tpar0015/4191-Robot/data/labelled/g_bl_ca_4.jpg

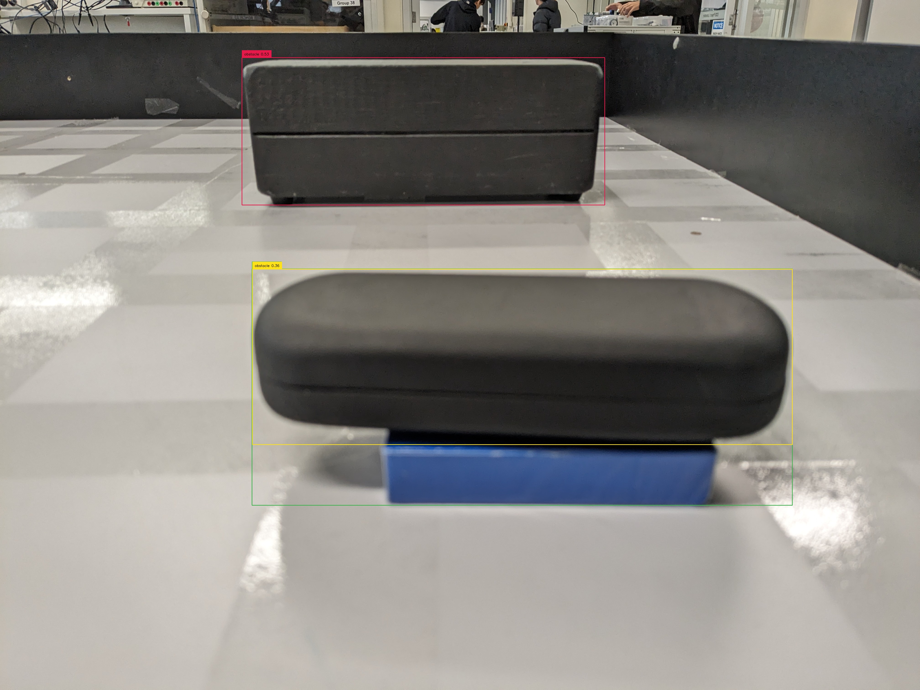
data/labelled/g_bl_ca_4.jpg
