tpar0015/4191-Robot/camera_img/camera3.jpg

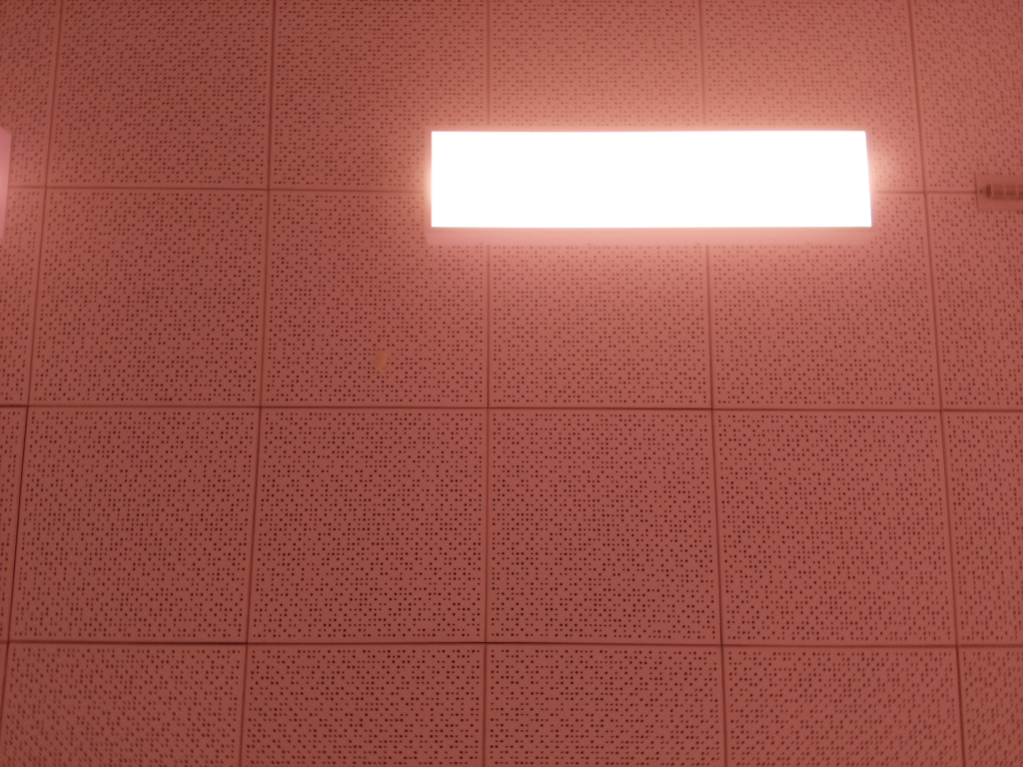
camera_img/camera3.jpg
