tpar0015/4191-Robot/camera_img/tes2/camera4.jpg

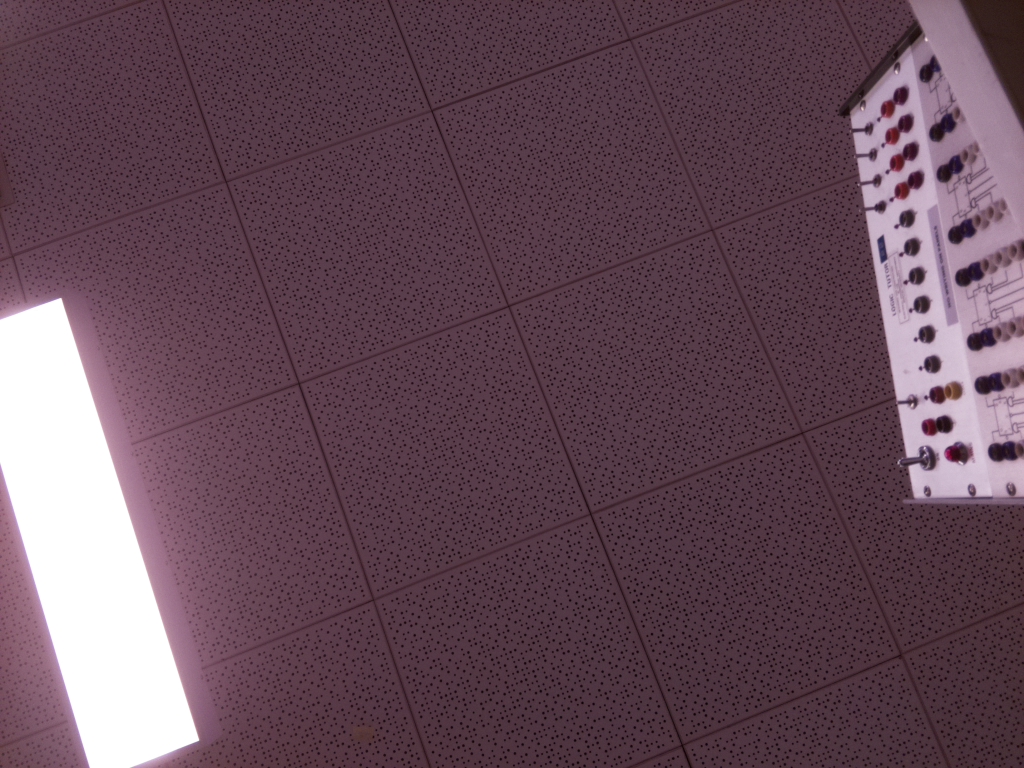
camera_img/tes2/camera4.jpg
