tpar0015/4191-Robot/Corner Detection/1.jpeg

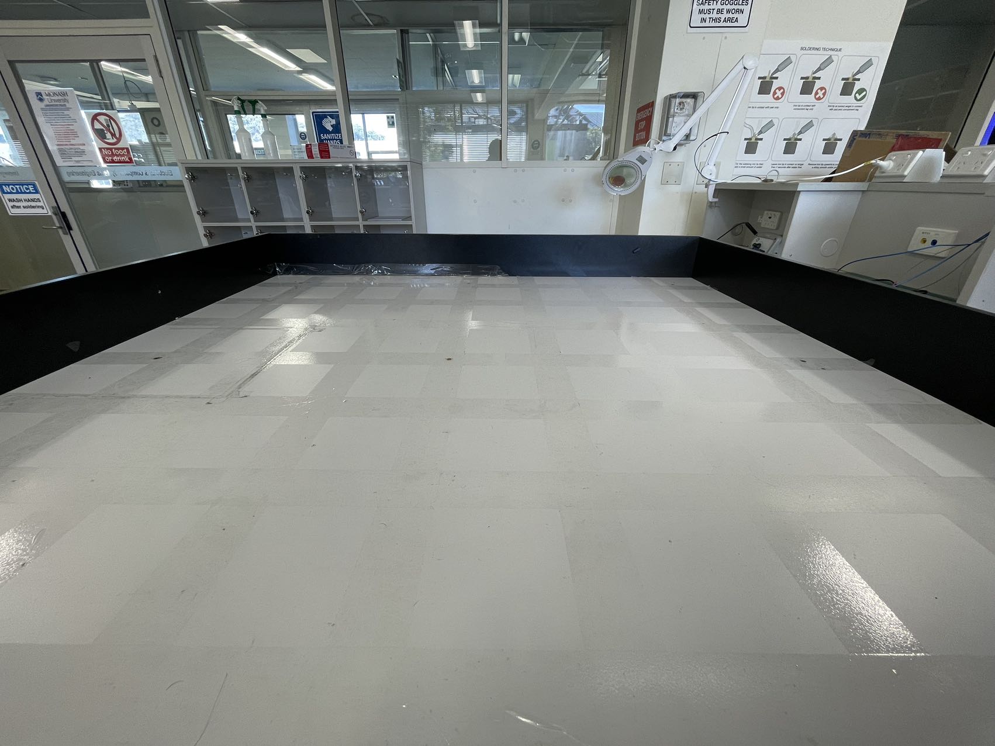
Corner Detection/1.jpeg
