tpar0015/4191-Robot/Corner Detection/arena_2.jpeg

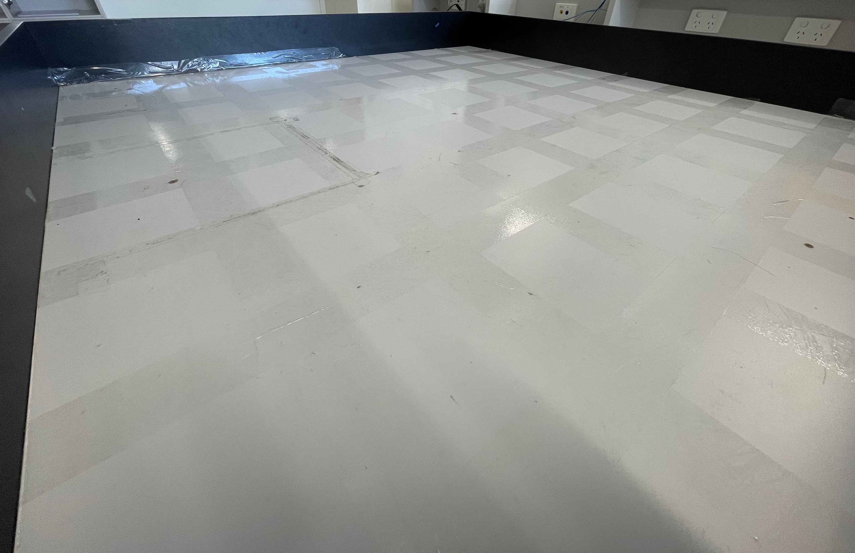
Corner Detection/arena_2.jpeg
