tpar0015/4191-Robot/Corner Detection/arena_3.jpeg

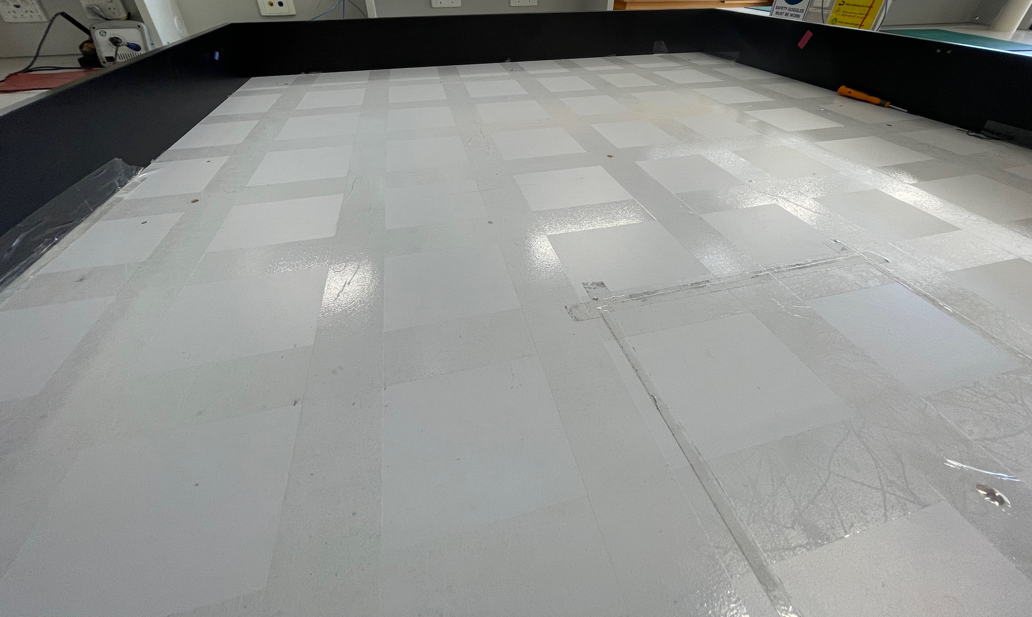
Corner Detection/arena_3.jpeg
