tpar0015/4191-Robot/Corner Detection/arena_notape2.jpg

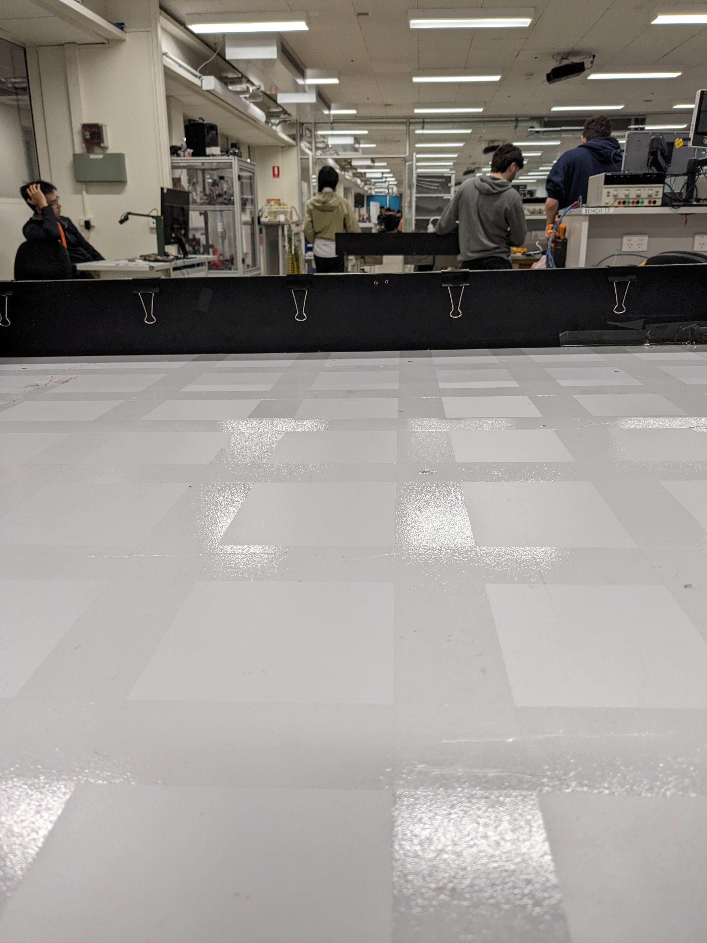
Corner Detection/arena_notape2.jpg
