tpar0015/4191-Robot/Corner Detection/arena_notape3.jpg

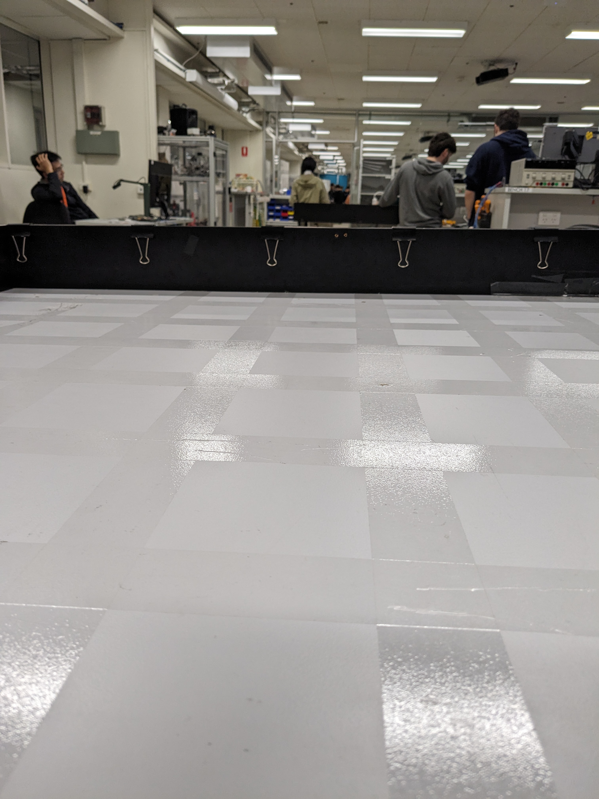
Corner Detection/arena_notape3.jpg
