tpar0015/4191-Robot/Corner Detection/arena_notape.jpg

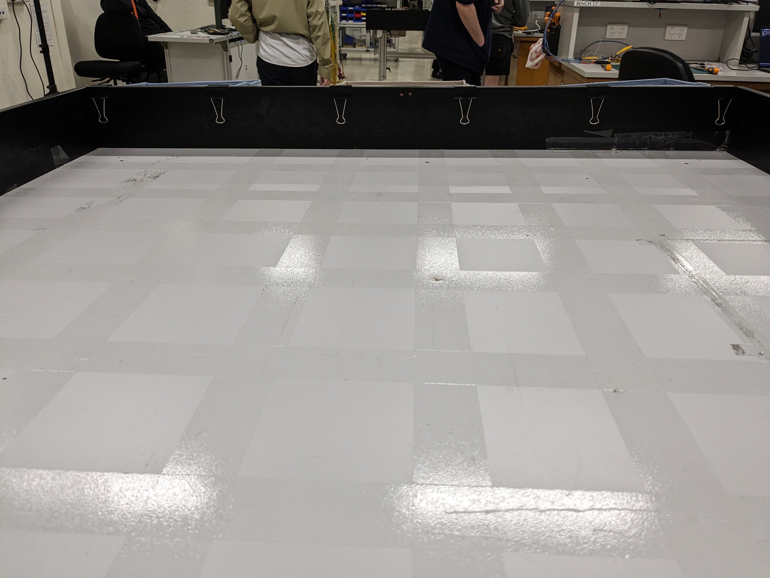
Corner Detection/arena_notape.jpg
