tpar0015/4191-Robot/Corner Detection/arena_tape_robot_centre.jpg

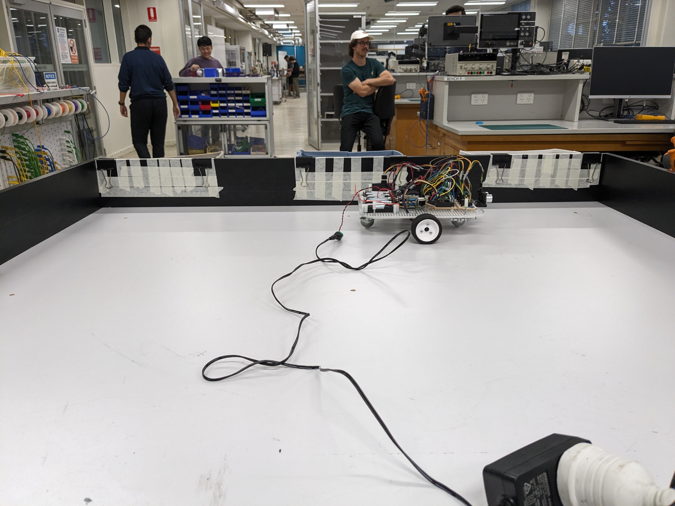
Corner Detection/arena_tape_robot_centre.jpg
