tpar0015/4191-Robot/Corner Detection/arena_wide.jpeg

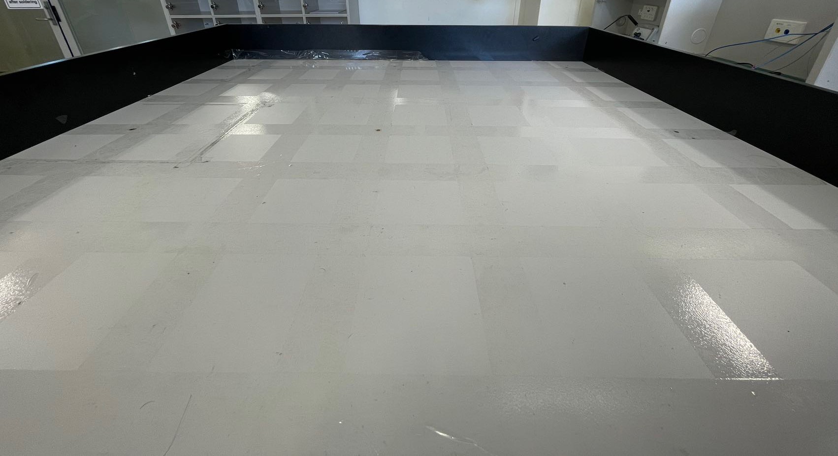
Corner Detection/arena_wide.jpeg
