tpar0015/4191-Robot/data/labelled/bl.jpg

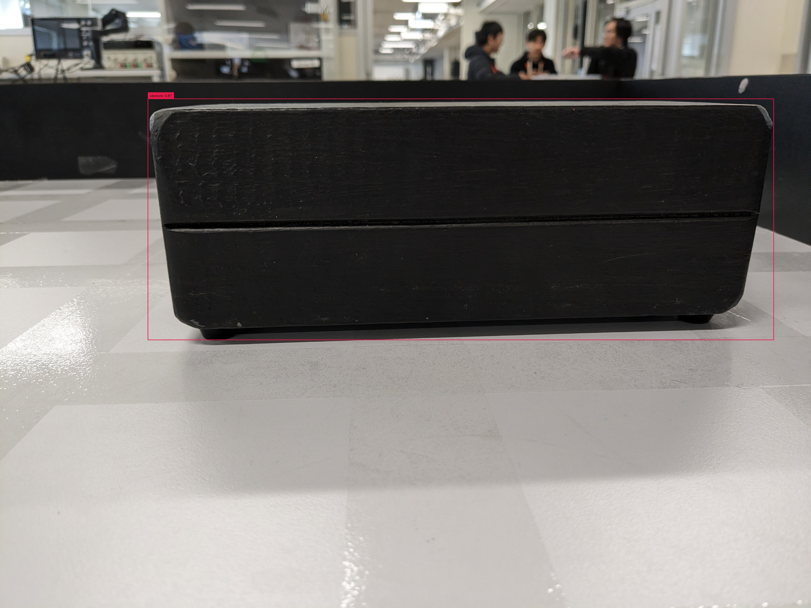
data/labelled/bl.jpg
