tpar0015/4191-Robot/data/labelled/bl_ca.jpg

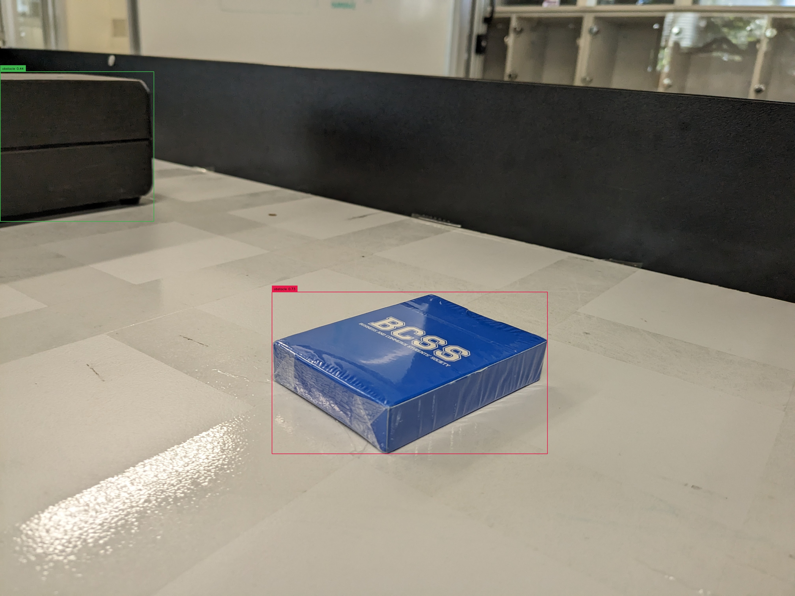
data/labelled/bl_ca.jpg
