tpar0015/4191-Robot/data/labelled/bl_ca_front.jpg

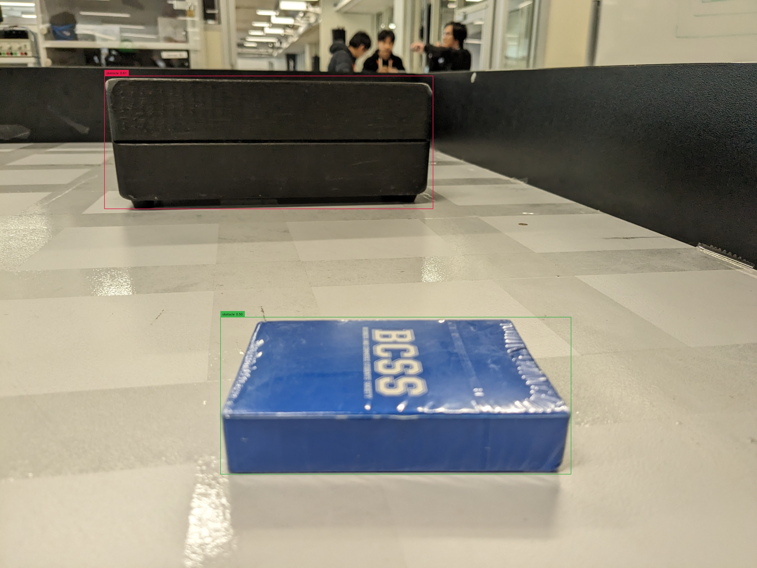
data/labelled/bl_ca_front.jpg
