tpar0015/4191-Robot/data/labelled/g_bl.jpg

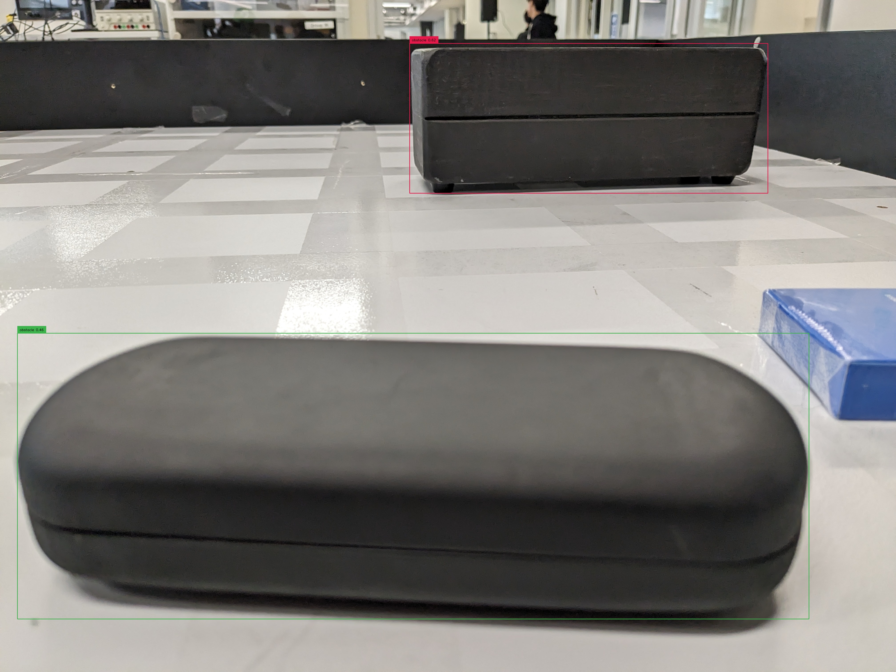
data/labelled/g_bl.jpg
