tpar0015/4191-Robot/data/labelled/g_bl_ca.jpg

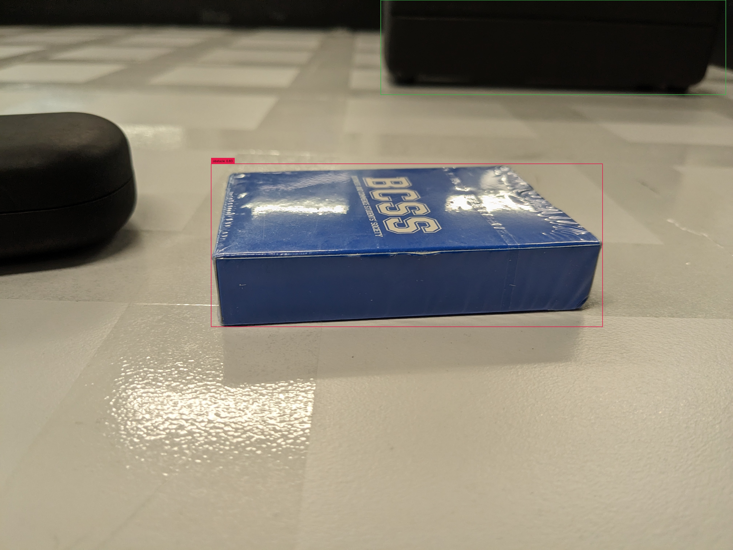
data/labelled/g_bl_ca.jpg
