tpar0015/4191-Robot/data/labelled/g_bl_ca_3.jpg

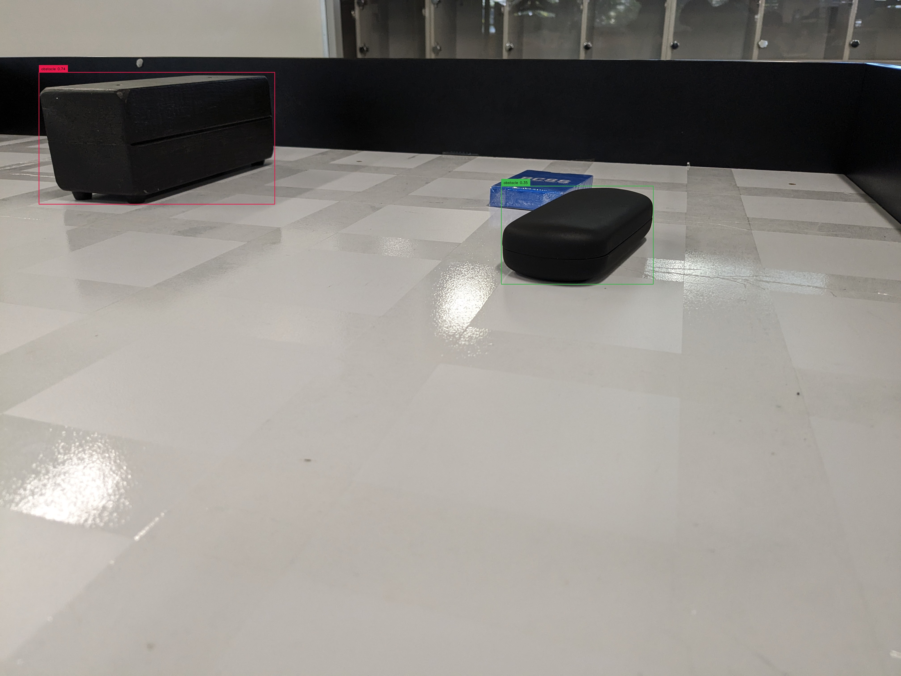
data/labelled/g_bl_ca_3.jpg
