tpar0015/4191-Robot/data/sample_arena.png

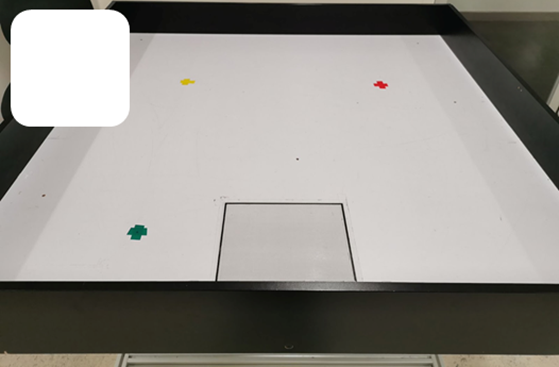
data/sample_arena.png
