tpar0015/4191-Robot/models/Veroboard/dual_H_bridge.png

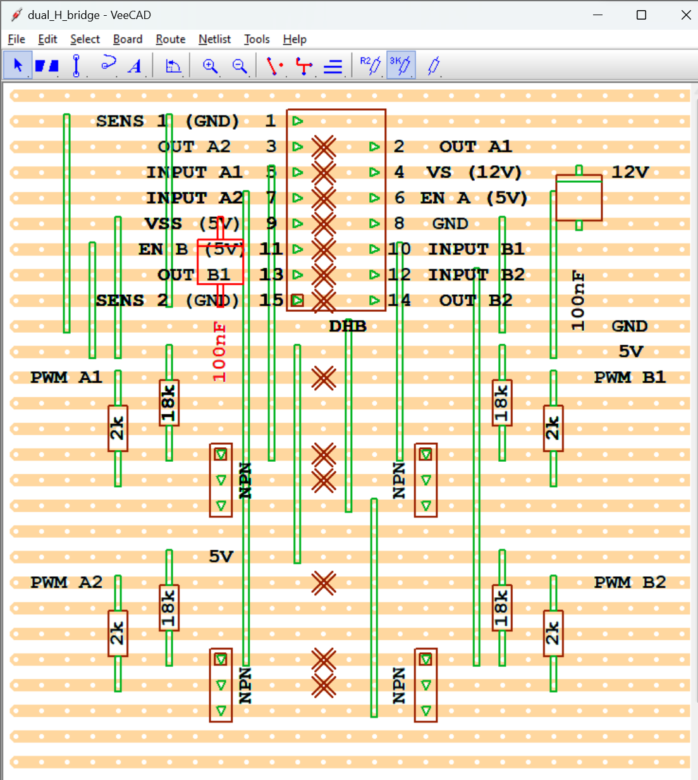
models/Veroboard/dual_H_bridge.png
