tpar0015/4191-Robot/models/Veroboard/electromagnet_circuit.png

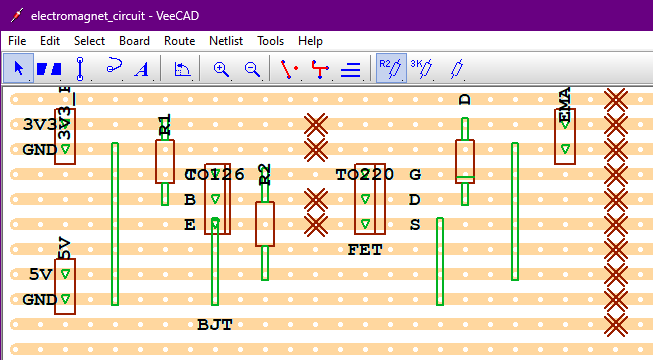
models/Veroboard/electromagnet_circuit.png
