tpar0015/4191-Robot/models/Veroboard/motor_circuit.png

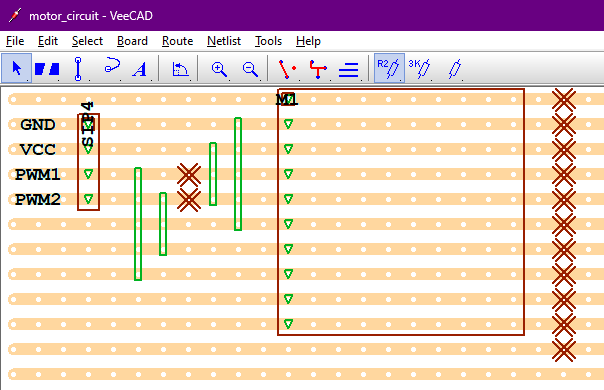
models/Veroboard/motor_circuit.png
