tpar0015/4191-Robot/models/Veroboard/powerboard.png

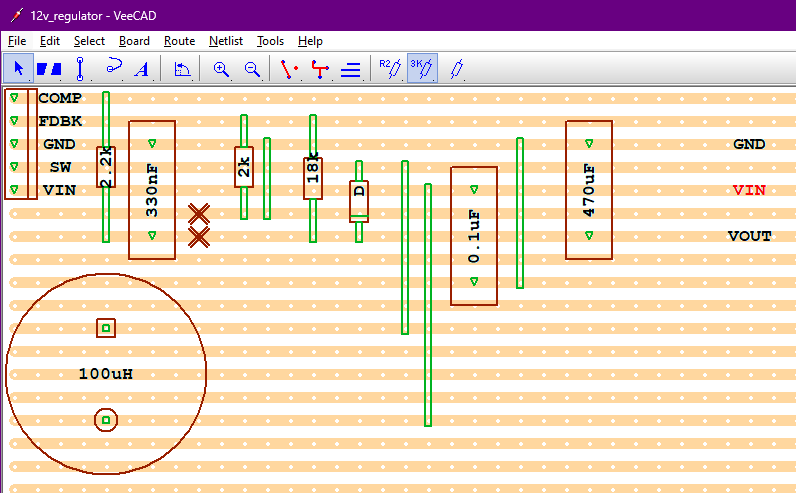
models/Veroboard/powerboard.png
