tpar0015/4191-Robot/Corner Detection/corner_detection.py

import numpy as np
import cv2
from matplotlib import pyplot as plt
import math

from picamera import PiCamera
from time import sleep


class DetectCorner:
    """
    Class module to detect corners and find angles
    """
    def __init__(self, robot_pos, arena_img):
        self.robot_pos = robot_pos
        self.corners = [[0,0],[0,0]]
        self.arena_img = arena_img

    def update_arena(self, time=1):
        camera = PiCamera()
        sleep(time)
        #camera.capture('/home/hanlinpi/Desktop/Project_4191/camera4.jpg')
        path = "Corner Detection/current.jpg"
        camera.capture(path)
        img = cv2.imread(path)
        img = cv2.resize(img, [2592, 1944])
        img = cv2.cv2Color(img, cv2.COLOR_BGR2GRAY)
        self.arena_img = img
        
    def get_corners(self):
        im = self.arena_img
        felt = (im >105)
        crop_line = float('nan')
        for i in range(felt.shape[0]):
            for j in range(felt.shape[1] - 800):
                if (np.sum(felt[i,j:j+800]) == 0):
                    crop_line = i
                    break
            if ~np.isnan(crop_line):
                break

        crop_image = felt[crop_line:,:]

        edges = cv2.Canny(crop_image.astype(np.uint8)*255,100,200)

        def ransac_line(image,N=1000,max_error=2, existing_line_threshold=5):

            good_lines = []
            consensus_list = []

            points_x,points_y = np.where(edges>0)
            points_homog = np.vstack([points_x,points_y,np.ones(len(points_x))]).T

            for j in range(N):

                bins = np.random.choice(len(points_x),2,replace=False)

                line = np.cross(points_homog[bins[0],:],points_homog[bins[1],:])

                line = line/np.sqrt(line[0]**2 + line[1]**2)

                line = line.reshape(1,3)

                consensus = np.sum((np.abs(np.sum(line*points_homog,axis=-1)) <= max_error))

                if len(good_lines) > 0:


                    # Check if line already found by comparing intercepts
                    c_good = -np.vstack(good_lines)[:,2]/(np.vstack(good_lines)[:,0]+1e-19)
                    c_line = -line[0,2]/(line[0,0]+1e-19)

                    d = np.abs(c_good-c_line)
                    best_d = np.argmin(d)

                    # Check if line alread exists
                    if (np.min(d) < existing_line_threshold):
                        #if better than current consensus, replace line
                        if (np.sum(d<existing_line_threshold)==1)&(consensus > consensus_list[best_d]): # existing line
                            good_lines[best_d] = line
                            consensus_list[best_d] = consensus

                    else:
                        # less than 4 lines - add a new one
                        if len(good_lines) < 3:
                            good_lines.append(line)
                            consensus_list.append(consensus)
                        # more than four lines, replace if better than worst line consensus
                        elif (consensus > np.min(np.array(consensus_list))):
                            worst_consensus = np.argmin(np.array(consensus_list))
                            good_lines[worst_consensus] = line
                            consensus_list[worst_consensus] = consensus

                else:
                    good_lines.append(line)
                    consensus_list.append(consensus)

            return good_lines, consensus_list

        lines,consensus_list = ransac_line(edges,N=5000,max_error=2,existing_line_threshold=100)

        x = np.linspace(0,edges.shape[0]-1,edges.shape[0],dtype=int)

        intercepts = []
        for l1 in lines:
            for l2 in lines:

                point = np.cross(l1,l2)
                point = point/(point[0,2]+1e-19)

                if (point[0,0]>0)&(point[0,1]>0)&(point[0,0]<edges.shape[0])&(point[0,1]<edges.shape[1]):
                    intercepts.append(point)

        intercepts = np.unique(np.vstack((intercepts)),axis=0)
        intercepts = intercepts[np.argsort(intercepts[:,0]),:]
        intercepts = np.int0(intercepts[:,:-1])
        intercepts[0,0] = intercepts[0,0]+crop_line
        intercepts[1,0] = intercepts[1,0]+crop_line

        print(intercepts)
        self.corners = intercepts

    def get_corner_angle(self, corner_no):
        """
        Corner points: [x, y]
        """
        robot_position = self.robot_pos
        corner = self.corners[corner_no]

        # Vector from robot pos to corner
        robot_to_corner_vec = (robot_position[0]-corner[0], robot_position[1]-corner[1])

        # Angle between robot pos and corner
        angle_rad = math.atan2(robot_to_corner_vec[1], robot_to_corner_vec[0])

        # Convert the angle from radians to degrees
        angle_deg = math.degrees(angle_rad)
        print(f"Angle between robot pos {robot_position} and corner {corner} is {angle_deg}")
        
        
if __name__ == "__main__":
    im = cv2.imread('1.jpeg')
    im = cv2.resize(im, [2592, 1944])
    im = cv2.cvtColor(im,cv2.COLOR_BGR2GRAY)

    robot_pos = (1250, 1250)
    corner_detector = DetectCorner(robot_pos, im)
    corner_detector.get_corners()
    corner_detector.get_corner_angle(0)
