tpar0015/4191-Robot/ultrasonic.py

"""
Author: Thomas Pardy
Date Modified: 2023-08-21
Ultrasonic sensor modules.
"""

import RPi.GPIO as GPIO
import time
from led import ledCRL
from pins import *
from multiprocessing import Queue

# 1. send singnal to ultrasonic sensor(trig) and sensor send signal to sense the distance
# 2. wait until sensor recieve the signal to calculate distance
# 3. calculate via formula
class Distance_Object:
    def __init__(self, distance):
        self.distance = distance
    
    def get_distance(self):
        return self.distance

class Ultrasonic:
    """
    Module for ultrasonic sensor
    """

    def __init__(self, trig, echo):
        self.trig_pin = trig
        self.echo_pin = echo
        self.led = ledCRL()
        self.distance = float('inf')
        self.time_out = (200 * 2 / 100 / 340 * 1e6)  # Max Distance*2 / 100 / 340 * 1e6 (11764.7058824)
        self.setup()

    def pulse(self, pin, toggle):
        """
        Return the length of the pulse (uS) or 0 if no pulse is returned before
        the timeout.
        """
        t0 = time.time()
        while GPIO.input(pin) != toggle:
            if time.time() - t0 > self.time_out * 1e-6:
                return 0
        t0 = time.time()
        while GPIO.input(pin) == toggle:
            if time.time() - t0 > self.time_out * 1e-6:
                return 0

        pulse_time = (time.time() - t0) * 1e6

        return pulse_time

    def get_sonar(self):
        """
        Return the measured distance of pulse in cm
        """
        GPIO.output(self.trig_pin, GPIO.HIGH)
        GPIO.output(self.trig_pin, GPIO.LOW)
        ping_time = self.pulse(self.echo_pin, GPIO.HIGH)
        distance = ping_time * 340 / 2 / 1e3  # speed of sound 340m/s
        self.distance = distance
    
    def get_distance(self) -> float:
        """Returns distance attribute"""
        return self.distance
    
    def setup(self):
        GPIO.setmode(GPIO.BCM)
        GPIO.setup(self.trig_pin, GPIO.OUT)
        GPIO.setup(self.echo_pin, GPIO.IN)

    def single_iteration(self):
        self.get_sonar()
        distance = self.get_distance()
        return distance
    def loop(self):
        while True:
            distance = self.single_iteration()
            print("Distance: %.2f mm" % (distance))
            time.sleep(1)

if __name__ == "__main__":
    ultrasonic = Ultrasonic(17,27)
    ultrasonic.loop()
