tpar0015/4191-Robot/pins.py

PINS = {
    "motor1_en": -1,  # Right Motor
    "motor1_a": 13,
    "motor1_b": 6,
    "motor2_en":26,
    "motor2_a": 16,    # Left Motor
    "motor2_b": 12,

    "motor3_a": 7,  # Drawback Motor
    "motor3_b": 8,

    "encoder1_a": 26,    # Right Encoder
    "encoder1_b": 19,
    "encoder2_a": 21,   # Left Encoder
    "encoder2_b": 20,
    
    "sonar_trig0": 24,
    "sonar_echo0": 23, 
    "electromagnet": 5
}
