tpar0015/4191-Robot/rotary.py

# Provides functions to stop motors depending on rotary encoder output
from gpiozero import RotaryEncoder


pin_rotary_a = 20    #? change later
pin_rotary_b = 21

rotor = RotaryEncoder(pin_rotary_a, pin_rotary_b, max_steps=0)

def printPosition():
    last_position = None
    while True:
        position = rotor.steps
        # if last_position == None or position != last_position:
        print(position)
        # last_position = position

# def stopAfterTicks(ticks, motor1="", motor2=""):
#     initialPosition = rotor.steps
#     diff = 0
#     while abs(diff) < ticks:
#         newPosition = rotor.steps
#         diff = newPosition - initialPosition
#     if motor1:
#         print("Stopping motor 1")
#         # motor1.off()
#     if motor2:
#         print("Stopping motor 2")
#         # motor2.off()
