tpar0015/4191-Robot/test_main.py

import time
from MotorControl.drive_new import Drive
from MotorControl.motorctl_new import Motor
from multiprocessing import Manager
from processing import MultiProcess
from pins import *
from electromagnet import Electromagnet
from camera_pyFile.QRdetect import readQR
import numpy as np
from aiming import aiming

class Control:
    def __init__(self):
        self.manager = Manager()
        self.position = {           
            "x": 0,             # Positive x is from loading zone to bins
            "y": 0,             # Positive y is left to right from loading zone side
            "angle": 0.0          # Positive angle is anticlockwise from the right (radians in (-pi,pi])
        }
        self.processes = MultiProcess(self.manager, ["drawback"])
        self.drive_control = Drive([0,0,0])
        self.electromagnet = Electromagnet(gpio_pin=PINS["electromagnet"])

        self.drawback_motor = Motor(-1, PINS["motor3_a"], PINS["motor3_b"])
        self.drawback_distance = 80         # drawback to fire
        self.ready_distance = self.drawback_distance + 10 # ready position ~70% of fire drawback
        self.package_holder_home = 168      # home position after firing
        self.ultrasonic_error = 10          # uncertainty in ultrasonic sensor distance reading

    # def get_bin_position(self, cam_result):
    #     match cam_result:
    #         case 1:  # Bin A
    #             return {"x": 130, "y": 0}
    #         case 2:  # Bin B
    #             return {"x": 130, "y": 60}
    #         case 3:  # Bin C
    #             return {"x": 130, "y": 120}
    #         case _:
    #             return None
        
    def testing(self):
        x = True
        while x:
            s = input('Forward done?  ')
            if s == 'y':
                x = False
            else:
                self.drawback_motor.set_speed(100)
                self.drawback_motor.forward()
                time.sleep(0.5)
                self.drawback_motor.stop()
            current_dist = self.processes.get_ultrasonic("drawback")
            print(current_dist)
        y = True
        while y:
            s = input("Drawback done? ")
            if s == 'y':
                y = False
            else:
                self.drawback_motor.set_speed(100)
                self.drawback_motor.backward()
                time.sleep(0.5)
                self.drawback_motor.stop()
                
            current_dist = self.processes.get_ultrasonic("drawback")
            print(current_dist)
        input('Release')
        self.electromagnet.turn_off()
        input('done')
        self.electromagnet.clean_up()

    def start(self):
        # Stage 0: Home and drawback 70%

        #  where the magnet is
        current_dist = self.processes.get_ultrasonic("drawback")

        # Draw forward to home position
        print("Drawing to home position")
        if current_dist < self.package_holder_home - self.ultrasonic_error:
            # Move to package holder
            dist_ready = 0  # count the number of times that ultrasonic output matches the desired location
            while dist_ready <= 5:
                #self.drawback_motor.set_speed(100)
                self.drawback_motor.forward()
                current_dist = self.processes.get_ultrasonic("drawback")
                if current_dist < self.package_holder_home - self.ultrasonic_error:
                    dist_ready += 1
            self.drawback_motor.stop()
            self.electromagnet.turn_on()

        # Drawback to ready position
        print("Drawing to ready position")
        if current_dist > self.ready_distance + self.ultrasonic_error:
            # Move to ready position
            while current_dist > self.ready_distance + self.ultrasonic_error:
                #self.drawback_motor.set_speed(100)
                self.drawback_motor.backward()
                current_dist = self.processes.get_ultrasonic("drawback")
            self.drawback_motor.stop()

        ##############################

        # Stage 1: Read QR code at camera
        cam_result = None

        while cam_result is None:
            cam_result = readQR()

        print("Read QR code with result", cam_result)

        ##############################
        # Stage 2: Orient towards bin
        bin_position = self.get_bin_position(cam_result)

        # Calculate required turn angle
        x_deviation = bin_position["x"] - self.position["x"]
        y_deviation = bin_position["y"] - self.position["y"]
        target_angle = np.arctan2(x_deviation, y_deviation)     # Note: order is this way because of direction convention

        #? TODO: Turn to target angle
        # Given target angle in theta
        self.drive_control.turn(target_angle)
        self.position["angle"] = target_angle
        ##############################
        # Stage 3: Drawback & Fire

        # Check where the magnet is
        current_dist = self.processes.get_ultrasonic("drawback")

        if self.ready_distance - self.ultrasonic_error < current_dist < self.ready_distance + self.ultrasonic_error:
            # Magnet is at ready position
            while current_dist > self.drawback_distance:
                #self.drawback_motor.set_speed(100)
                self.drawback_motor.backward()
                current_dist = self.processes.get_ultrasonic("drawback")
            self.drawback_motor.stop()
            # Fire
            self.electromagnet.turn_off()
        ##############################
        # Stage 4: Orient to home position 
        
        #? TODO: Return robot to initial pose
        target_angle = np.pi/2
        self.drive_control.turn(target_angle)
        self.position["angle"] = target_angle

        pass 
        # self.drive_control.drive_forward(-1)

    def start_noaim(self):
        # Stage 0: Home and drawback 70%

        #  where the magnet is
        current_dist = self.processes.get_ultrasonic("drawback")

        # Draw forward to home position
        print("Drawing to home position")
        if current_dist < self.package_holder_home - self.ultrasonic_error:
            # Move to package holder
            dist_ready = 0  # count the number of times that ultrasonic output matches the desired location
            while dist_ready <= 5:
                #self.drawback_motor.set_speed(100)
                self.drawback_motor.forward()
                current_dist = self.processes.get_ultrasonic("drawback")
                if current_dist < self.package_holder_home - self.ultrasonic_error:
                    dist_ready += 1
            self.drawback_motor.stop()
            self.electromagnet.turn_on()

        # Drawback to ready position
        print("Drawing to ready position")
        if current_dist > self.ready_distance + self.ultrasonic_error:
            # Move to ready position
            while current_dist > self.ready_distance + self.ultrasonic_error:
                #self.drawback_motor.set_speed(100)
                self.drawback_motor.backward()
                current_dist = self.processes.get_ultrasonic("drawback")
            self.drawback_motor.stop()

        ##############################

        # Stage 1: Read QR code at camera
        cam_result = None

        while cam_result is None:
            cam_result = readQR()

        print("Read QR code with result", cam_result)

        ##############################
        # Stage 2: Orient towards bin
        #bin_position = self.get_bin_position(cam_result)
        if cam_result == 3:
            print("shooting at bin C")
            self.electromagnet.turn_off()
        elif cam_result == 2:
            print("shooting at bin B")
            self.electromagnet.turn_off()
        elif cam_result == 1:
            print("shooting at bin A")
            self.electromagnet.turn_off()

        

if __name__ == "__main__":
    with Manager() as manager:
        processes = MultiProcess(manager, ["drawback"])
        processes.start_processes()

        robot = Control()

        while True:
            # distance = processes.get_ultrasonic("drawback")
            # print("Distance: %.2f mm" % (distance))
            # time.sleep(0.2)

            #robot.start()
            #robot.start_noaim()
            robot.testing()
