tpar0015/4191-Robot/Test/BaseClasses.py

import RPi.GPIO as GPIO
from time import sleep, time
import math

def calculate_distance_between_points(point_1=None, point_2=None):
    return math.sqrt((point_1.x - point_2.x) ** 2 + (point_1.y - point_2.y) ** 2)

def do_segments_intersect(segment1=None, segment2=None):
    p1, q1 = segment1.start, segment1.end
    p2, q2 = segment2.start, segment2.end

    # Find the 4 orientations required for
    # the general and special cases
    o1 = intersection_orientation(p1, q1, p2)
    o2 = intersection_orientation(p1, q1, q2)
    o3 = intersection_orientation(p2, q2, p1)
    o4 = intersection_orientation(p2, q2, q1)

    # General case
    if (o1 != o2) and (o3 != o4):
        return True

    # Special Cases

    # p1 , q1 and p2 are collinear and p2 lies on segment p1q1
    if (o1 == 0) and onSegment(p1, p2, q1):
        return True

    # p1 , q1 and q2 are collinear and q2 lies on segment p1q1
    if (o2 == 0) and onSegment(p1, q2, q1):
        return True

    # p2 , q2 and p1 are collinear and p1 lies on segment p2q2
    if (o3 == 0) and onSegment(p2, p1, q2):
        return True

    # p2 , q2 and q1 are collinear and q1 lies on segment p2q2
    if (o4 == 0) and onSegment(p2, q1, q2):
        return True

    # If none of the cases
    return False

def intersection_orientation(p, q, r):
    # To find the orientation of an ordered triplet (p,q,r)

    val = round(((q.y - p.y) * (r.x - q.x)) - ((q.x - p.x) * (r.y - q.y)), 10)
    if val > 0:
        # Clockwise orientation
        return 1
    elif val < 0:
        # Counterclockwise orientation
        return 2
    else:
        # Collinear orientation
        return 0

def onSegment(p, q, r):
    if ((q.x <= max(p.x, r.x)) and (q.x >= min(p.x, r.x)) and
            (q.y <= max(p.y, r.y)) and (q.y >= min(p.y, r.y))):
        return True
    return False

def find_segment_intersection(segment1, segment2):
    xdiff = Pose(segment1.start.x - segment1.end.x, segment2.start.x - segment2.end.x)
    ydiff = Pose(segment1.start.y - segment1.end.y, segment2.start.y - segment2.end.y)

    def det(a, b):
        return a.x * b.y - a.y * b.x

    div = det(xdiff, ydiff)
    if div == 0:
        return None

    d = Pose(det(segment1.start, segment1.end), det(segment2.start, segment2.end))
    x = det(d, xdiff) / div
    y = det(d, ydiff) / div
    return Pose(x, y)

def create_point(point=None, dist=None, angle=None):
    return Pose(point.x + dist * math.cos(angle), point.y + dist * math.sin(angle))

class Pose:
    def __init__(self, x=None, y=None, theta=None):
        self.x = x  # x coordinate of objects pose
        self.y = y  # y coordinate of objects pose
        self.theta = theta  # The angle the object is "facing" measured counter-clockwise from the positive x-axis.

class Segment:
    def __init__(self, start_point=None, end_point=None):
        self.start = start_point
        self.end = end_point

    def length(self):
        return calculate_distance_between_points(self.start, self.end)

class Polygon:
    def __init__(self, vertices=None):
        self.vertices = vertices  # List of Point instances
        self.maximum = self.calculate_maximum_length()
        self.segments = self.calculate_segments()
        self.count = self.calculate_count()
        self.centroid = self.calculate_centroid()

    def calculate_centroid(self):
        x_sum = 0
        y_sum = 0
        for vertex in self.vertices:
            x_sum += vertex.x
            y_sum += vertex.y
        x_avg = x_sum / self.count
        y_avg = y_sum / self.count
        centroid = Pose(x_avg, y_avg)
        return centroid

    def calculate_maximum_length(self):
        max_length = 0
        for vertex1_index in range(len(self.vertices)):
            for vertex2_index in range(len(self.vertices) - 1):
                if vertex1_index == vertex2_index:
                    continue
                vertex1 = self.vertices[vertex1_index]
                vertex2 = self.vertices[vertex2_index]
                length = calculate_distance_between_points(vertex1, vertex2)
                if length > max_length:
                    max_length = length
        return max_length

    def calculate_segments(self):
        segments = []
        for index in range(len(self.vertices)):
            vertex1 = self.vertices[index]
            vertex2 = self.vertices[(index + 1) % len(self.vertices)]
            new_segment = Segment(vertex1, vertex2)
            segments.append(new_segment)
        return segments

    def calculate_count(self):
        count = len(self.vertices)
        return count

    def contains(self, point=None):
        # Cast ray to the right and count how many intersections
        ray_end = create_point(point, self.maximum, 0)
        ray = Segment(point, ray_end)
        intersection_count = 0
        intersections = []
        for segment in self.segments:
            if do_segments_intersect(ray, segment):
                intersection_count += 1
                intersections.append(find_segment_intersection(ray, segment))

        # If no intersections, point not in the polygon
        if intersection_count == 0:
            return False

        # Filter out duplicate points
        indices_to_remove = []
        for index1, point1 in enumerate(intersections):
            for index2, point2 in enumerate(intersections):
                if index1 != index2 and point1.equals(point2):
                    indices_to_remove.append(index1)

        indices_to_remove.sort()
        for index in indices_to_remove:
            intersections.pop(index)

        # If odd intersection count, point is contained by polygon
        if intersection_count % 2 != 0:
            return True

        # If even intersection count, point is not with polygon
        return False

class Obstacle:
    def __init__(self, boundary=None, tolerance=None):
        self.boundary = boundary  # A polygon class that makes the bounding box of the obstacle
        self.tolerance = tolerance  # The distance in metres the robot is allowed to the bounding box of the obstacle

class Path:
    def __init__(self):
        self.waypoint_queue = None

class Package:
    def __init__(self, colour=None):
        self.colour = colour  # A unique id number for a destination e.g: "red", "green", "blue"
        self.destination_pose = None
        self.identify_destination()

    def identify_destination(self):
        if self.colour == "red":
            self.destination_pose = Pose(x=0.25, y=1.3, theta=math.pi/2)
        if self.colour == "green":
            self.destination_pose = Pose(x=0.75, y=1.3, theta=math.pi/2)
        if self.colour == "blue":
            self.destination_pose = Pose(x=1.25, y=1.3, theta=math.pi/2)

class Motor:
    def __init__(self, enable_pin=None, input_a=None, input_b=None, encoder_a=None, encoder_b=None, speed=100):
        self.enable_pin = enable_pin
        self.input_a = input_a
        self.input_b = input_b
        self.encoder_a = encoder_a
        self.encoder_b = encoder_b
        GPIO.setup(self.enable_pin, GPIO.OUT)
        GPIO.setup(self.input_a, GPIO.OUT)
        GPIO.setup(self.input_b, GPIO.OUT)
        GPIO.setup(self.encoder_a, GPIO.IN)
        GPIO.setup(self.encoder_b, GPIO.IN)
        self.speed = speed  # Speed from 0 to 100
        self.pwm = GPIO.PWM(self.enable_pin, 1000)
        self.pwm.start(self.speed)
        self.ticks = 0
        self.encoder_state = self.read_encoder()

    def set_speed(self, speed=None):
        self.speed = speed
        self.pwm.ChangeDutyCycle(speed)

    def forward(self):
        GPIO.output(self.input_a, GPIO.HIGH)
        GPIO.output(self.input_b, GPIO.LOW)

    def backward(self):
        GPIO.output(self.input_a, GPIO.LOW)
        GPIO.output(self.input_b, GPIO.HIGH)

    def stop(self):
        GPIO.output(self.input_a, GPIO.LOW)
        GPIO.output(self.input_b, GPIO.LOW)

    def read_encoder(self):
        encoder_a_reading = GPIO.input(self.encoder_a)
        encoder_b_reading = GPIO.input(self.encoder_b)
        new_state = (encoder_a_reading, encoder_b_reading)
        return new_state

    def reset_encoder(self):
        self.ticks = 0
        new_state = self.read_encoder()
        self.encoder_state = new_state

    def update_encoder(self):
        new_state = self.read_encoder()

        # Compare states
        if new_state != self.encoder_state:
            self.encoder_state = new_state
            self.ticks += 1

class ColourSensor:
    def __init__(self, s0, s1, s2, s3, signal):
        self.s0 = s0
        self.s1 = s1
        self.s2 = s2
        self.s3 = s3
        self.signal = signal
        self.num_of_cycles = 10

    def read_colour(self):
        red_count = 0
        green_count = 0
        blue_count = 0
        for index in range(5):
            # Read each colour sensor
            self.read_red()
            red_reading = self.single_reading()

            self.read_green()
            green_reading = self.single_reading()

            self.read_blue()
            blue_reading = self.single_reading()

            if red_reading > 20000 or green_reading > 20000 or blue_reading > 20000:
                # Find the largest
                if red_reading > green_reading and red_reading > blue_reading:
                    red_count += 1
                if green_reading > red_reading and green_reading > blue_reading:
                    green_count += 1
                if blue_reading > green_reading and blue_reading > red_reading:
                    blue_count += 1

        if red_count == 0 and blue_count == 0 and green_count == 0:
            return None

        # Find which colour shows up most
        if red_count > green_count and red_count > blue_count:
            return "red"
        elif green_count > blue_count and green_count > red_count:
            return "green"
        else:
            return "blue"

    def read_red(self):
        GPIO.output(self.s2, GPIO.LOW)
        GPIO.output(self.s3, GPIO.LOW)

    def read_green(self):
        GPIO.output(self.s2, GPIO.HIGH)
        GPIO.output(self.s3, GPIO.HIGH)

    def read_blue(self):
        GPIO.output(self.s2, GPIO.LOW)
        GPIO.output(self.s3, GPIO.HIGH)

    def single_reading(self):
        start_time = time()
        for impulse_count in range(self.num_of_cycles):
            GPIO.wait_for_edge(self.signal, GPIO.FALLING)
        signal_duration = time() - start_time
        reading_value = self.num_of_cycles / signal_duration
        return reading_value

# Measure distance
class Ultrasonic:
    
    def __init__(self, trig_pin = None, echo_pin = None):
        self.trig_pin = trig_pin
        self.echo_pin = echo_pin
        GPIO.setup(self.trig_pin, GPIO.OUT)
        GPIO.setup(self.echo_pin, GPIO.IN)

    def measure_dist(self):
        GPIO.output(self.trig_pin, True)
        sleep(0.00001)
        GPIO.output(self.trig_pin, False)

        while GPIO.input(self.echo_pin) == 0:
            pulse_start = time.time()

        while GPIO.input(self.echo_pin) == 1:
            pulse_end = time.time()

        pulse_duration = pulse_end - pulse_start
        distance = pulse_duration * 17150  # Speed of sound in cm/s

        return distance
